Fbn-lab/Power_bank/images/img1.JPG

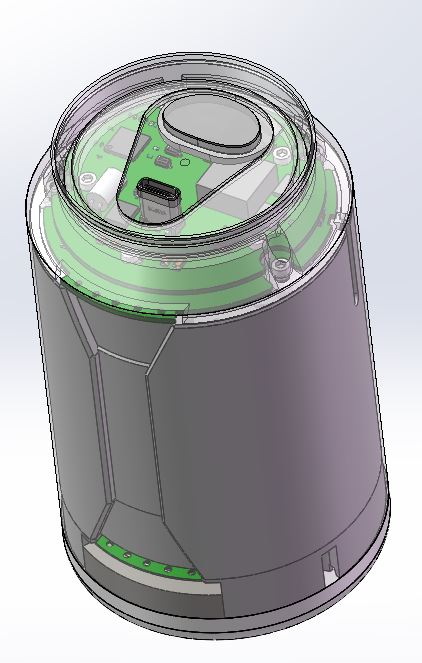
images/img1.JPG
