Fbn-lab/Power_bank/images/img2.jpg

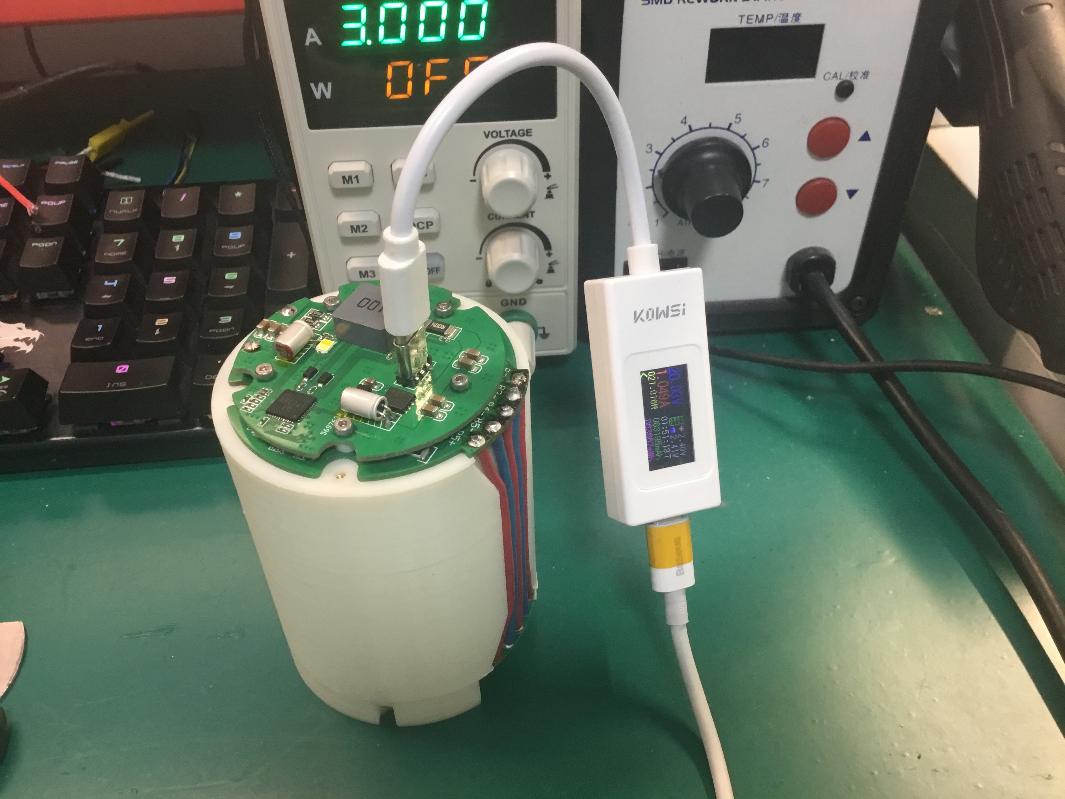
images/img2.jpg
