Fbn-lab/Power_bank/images/img3.jpg

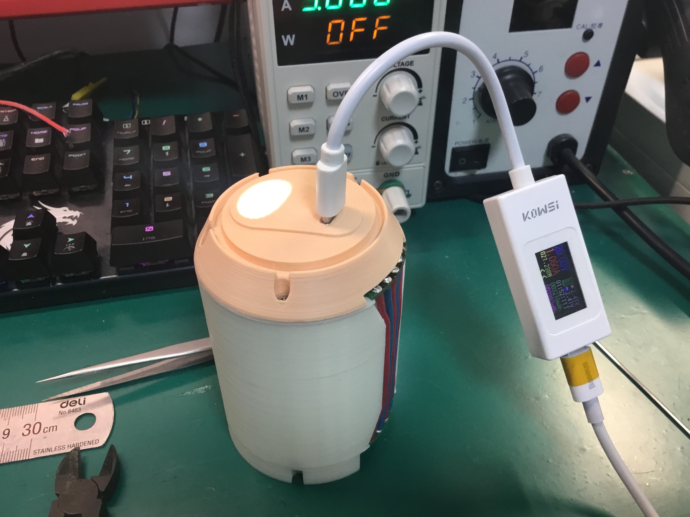
images/img3.jpg
