Fbn-lab/Power_bank/images/img4.jpg

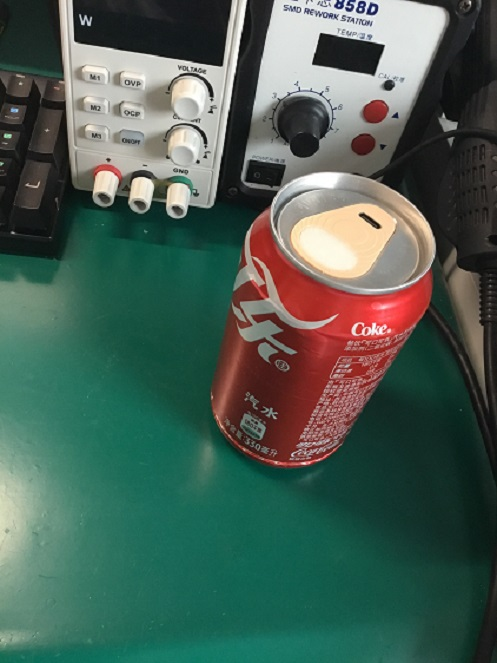
images/img4.jpg
